npetersen2/OpenThermo/firmware/openThermo/Core/Src/drv_tmp117.c

#include "drv_tmp117.h"
#include "drv_i2c.h"
#include "drv_tmp117_registers.h"
#include <stdbool.h>

static uint8_t _deviceAddress;   // Address of Temperature sensor

static uint16_t readRegister(uint8_t reg);				// Reads 2 register bytes from sensor
static void writeRegister(uint8_t reg, uint16_t data);	// Wires single byte of data to the sensor

#define bitRead(value, bit) (((value) >> (bit)) & 0x01)
#define bitSet(value, bit) ((value) |= (1UL << (bit)))
#define bitClear(value, bit) ((value) &= ~(1UL << (bit)))
#define bitWrite(value, bit, bitvalue) (bitvalue ? bitSet(value, bit) : bitClear(value, bit))

void drv_tmp117_init(void)
{
	  // Check to see if sensor is alive
	  bool working = drv_tmp117_begin(0x48);
	  if (!working) {
		  while(1);
	  }
	  drv_tmp117_setConversionCycleBit(0);
	  drv_tmp117_setConversionAverageMode(2);
}


/* BEGIN
    This function checks if the TMP will ACK over I2C, and
	if the TMP will correctly self-identify with the proper
	device ID. This will set the address of the device along
	with setting the wire for the I2C Communication.
	This will return true if both checks pass.
*/
bool drv_tmp117_begin(uint8_t sensorAddress)
{
	_deviceAddress = sensorAddress; // Sets the address of the device

	uint16_t deviceID = readRegister(TMP117_DEVICE_ID); // reads registers into rawData

	//make sure the device ID reported by the TMP is correct
	//should always be 0x0117
	if (deviceID != DEVICE_ID_VALUE)
	{
		return false;
	}

	return true; //returns true if all the checks pass
}

/* GET ADDRESS
	This function returns the address of the device once
	called upon. This address can only be 0x48 (GND),
	0x49 (V+), 0x4A (SDA), and 0x4B (SCL)
*/
uint8_t drv_tmp117_getAddress(void)
{
	return _deviceAddress;
}

/* READ REGISTER
	This function reads the register bytes from the sensor when called upon.
	This reads 2 bytes of information from the 16-bit registers.
*/
static uint16_t readRegister(uint8_t reg)
{
	// Start by sending register across bus
	drv_i2c_tx(_deviceAddress<<1, &reg, 1);

	// Read two bytes
	uint8_t data[2] = {0};
	drv_i2c_rx(_deviceAddress<<1, data, 2);

	// Swap the LSB and the MSB
	int16_t ret = 0;
	ret = ((data[0] << 8) | data[1]);

	return ret;
}


/* WRITE REGISTER
    Wire data to a TMP117 register
*/
static void writeRegister(uint8_t reg, uint16_t data)
{
	uint8_t highByte = (data >> 8) & 0xFF;
	uint8_t lowByte = (data & 0xFF);

	drv_i2c_tx(_deviceAddress<<1, &reg, 1);
	drv_i2c_tx(_deviceAddress<<1, &highByte, 1); // Write MSB (D15-D8)
	drv_i2c_tx(_deviceAddress<<1, &lowByte, 1); // Write LSB (D7-D0)
}


/* READ TEMPERATURE CELSIUS
	This function reads the temperature reading from the sensor
	and returns the value in degrees celsius.
	NOTE: The data type of digitalTemp is a signed integer, meaning that the
	value of the binary number being read will be negative if the MSB is 1,
	and positive if the bit is 0.
*/
float drv_tmp117_readTempC(void)
{
	int16_t digitalTempC = readRegister(TMP117_TEMP_RESULT); // Calls to read registers to pull all the bits to store in an array

	float finalTempC = digitalTempC * TMP117_RESOLUTION; // Multiplies by the resolution for digital to final temp

	return finalTempC;
}

/* READ TEMPERATURE FAHRENHEIT
	This function calculates the fahrenheit reading from the
	celsius reading initially found.
	The device reads in celsius unless this function is called.
*/
float drv_tmp117_readTempF(void)
{
	return drv_tmp117_readTempC() * 9.0f / 5.0f + 32.0f; // Conversion from °C to °F
}

/* GET TEMPERATURE OFFSET
	This function reads the temperature offset. This reads from the register
	value 0x07 (TMP117_TEMP_OFFSET). This can be found on page 23 of the
	datasheet.
*/
float drv_tmp117_getTemperatureOffset(void)
{
	int16_t _offset = 0;
	_offset = readRegister(TMP117_TEMP_OFFSET);				// Reads from the temperature offset register
	float finalOffset = (float)_offset * TMP117_RESOLUTION; // Multiplies by the resolution for correct offset temperature
	return finalOffset;
}

/* SET TEMPERATURE OFFSET
	This function sets the offset temperature of the device. The user
	can write to this to set any desired offset within the temperature range.
	This writes to the register value 0x07 (TMP117_TEMP_OFFSET)
*/
void drv_tmp117_setTemperatureOffset(float offset)
{
	int16_t resolutionOffset = offset / TMP117_RESOLUTION; // Divides by the resolution to send the correct value to the sensor
	writeRegister(TMP117_TEMP_OFFSET, resolutionOffset);   // Writes to the offset temperature register with the new offset value
}

/* GET LOW LIMIT
	This function reads the low limit register that is set by the user.
	The values are signed integers since they can be negative.
*/
float drv_tmp117_getLowLimit(void)
{
	int16_t lowLimit = 0;
	lowLimit = readRegister(TMP117_T_LOW_LIMIT);			// Calls to read register to pull all the bits to store in a variable
	float finalLimit = (float)lowLimit * TMP117_RESOLUTION; // Multiplies by the resolution for correct offset temperature
	return finalLimit;
}

/* SET LOW LIMIT
	This function allows the user to set the low limit register to whatever
	specified value, as long as in the range for the temperature sensor. This
	function can be used as a threshold for Therm mode and or Alert mode.
	The values are signed integers since they can be negative.
*/
void drv_tmp117_setLowLimit(float lowLimit)
{
	int16_t finalLimit = lowLimit / TMP117_RESOLUTION; // Divides by the resolution to send the correct value to the sensor
	writeRegister(TMP117_T_LOW_LIMIT, finalLimit);	 // Writes to the low limit temperature register with the new limit value
}

/* GET HIGH LIMIT
	This function reads the high limit register that is set by the user.
	The values are signed integers since they can be negative.
*/
float drv_tmp117_getHighLimit(void)
{
	int16_t highLimit = 0;
	highLimit = readRegister(TMP117_T_HIGH_LIMIT);			 // Calls to read registers to pull all the bits to store in an array
	float finalLimit = (float)highLimit * TMP117_RESOLUTION; // Multiplies by the resolution for correct offset temperature
	return finalLimit;
}

/* SET HIGH LIMIT
	This function allows the user to set the high limit register to whatever
	specified value, as long as in the range for the temperature sensor. This
	function can be used as a threshold for Therm mode and or Alert mode
	The values are signed integers since they can be negative.
*/
void drv_tmp117_setHighLimit(float highLimit)
{
	int16_t finalLimit = highLimit / TMP117_RESOLUTION; // Divides by the resolution to send the correct value to the sensor
	writeRegister(TMP117_T_HIGH_LIMIT, finalLimit);		// Writes to the high limit temperature register with the new limit value
}

/*GET CONFIGURATION REGISTER
	This function reads configuration register. Use this function if you need to read
	certain flags before they are cleared. This can be found on page 25 of the
	datasheet.
*/
uint16_t drv_tmp117_getConfigurationRegister(void)
{
	uint16_t configReg = 0;
	configReg = readRegister(TMP117_CONFIGURATION);

	return configReg;
}

/*GET HIGH AND LOW ALERT
	This function reads configuration register and saves the high and low alert flags.
	Use this function if you need to read the alert flags before they are cleared.
	This can be found on page 25 of the datasheet.
*/
uint8_t drv_tmp117_getHighLowAlert(void)
{
	uint16_t configReg = 0;
	configReg = readRegister(TMP117_CONFIGURATION); //Grab what is in the configuration register

	uint8_t highlowAlert = 0; //temporary variable to hold high and low alert flags
	//Get high alert flag from 15th bit of the configuration register,
	//    then write bit to highlowAlert's 2nd position from the right
	bitWrite(highlowAlert, 1, bitRead(configReg, 15));

	//Get high alert flag from 14th bit of the configuration register,
	//    then write bit to highlowAlert's 1st position from the right
	bitWrite(highlowAlert, 0, bitRead(configReg, 14));

	return highlowAlert; //return high and low alert flags
}

/*GET HIGH ALERT
	This function reads the 15th bit of the configuration register to
	tell if the conversion result is higher than the high limit. This
	is set as a High Alert flag. This can be found on page 25 of the
	datasheet.
*/
bool drv_tmp117_getHighAlert(void)
{
	uint16_t configReg = 0;
	configReg = readRegister(TMP117_CONFIGURATION); //Grab what is in the configuration register

	uint8_t highAlert = bitRead(configReg, 15); // Fills with the 15th bit of the configuration register

	if (highAlert == 1)
	{
		return true;
	}
	else
	{
		return false;
	}
}

/*GET LOW ALERT
	This function reads the 14th bit of the configuration register to
	tell if the conversion result is lower than the low limit. This
	is set as a Low Alert flag. This can be found on page 25 of the
	datasheet.
*/
bool drv_tmp117_getLowAlert(void)
{
	uint16_t configReg = 0;
	configReg = readRegister(TMP117_CONFIGURATION); //Grab what is in the configuration register

	uint8_t lowAlert = bitRead(configReg, 14); // Fills with the 14th bit of the configuration register

	if (lowAlert == 1)
	{
		return true;
	}
	else
	{
		return false;
	}
}

/*SET ALERT FUNCTION MODE
	This function sets the alert function mode to either "alert" or
	"therm" mode. This can be found on page 25 of the datasheet.
*/
void drv_tmp117_setAlertFunctionMode(uint8_t setAlertMode)
{
	uint16_t AlertFunctionMode = 0;
	AlertFunctionMode = readRegister(TMP117_CONFIGURATION); // Fills mode to be the config register

	if (setAlertMode == 1) // 1: Therm mode
	{
		bitWrite(AlertFunctionMode, 4, 1); //set register bit to be 1
		writeRegister(TMP117_CONFIGURATION, AlertFunctionMode);
	}
	else // 0: alert mode
	{
		bitClear(AlertFunctionMode, 4); //set register bit to be 0
		writeRegister(TMP117_CONFIGURATION, AlertFunctionMode);
	}
}

/*GET ALERT FUNCTION MODE
	This function gets the alert function mode to either "alert" or
	"therm" mode. This can be found on page 25 of the datasheet.
*/
uint8_t drv_tmp117_getAlertFunctionMode(void)
{
	uint16_t configReg = 0;
	configReg = readRegister(TMP117_CONFIGURATION); // Fill configReg with the configuration register

	uint8_t currentAlertMode = bitRead(configReg, 4); //Get the value from the Therm/alert mode ("T/nA") select field

	if (currentAlertMode == 1) //if "therm" mode
	{
		return 1;
	}
	else //if "alert" mode
	{
		return 0;
	}
}

/* SOFTWARE RESET
	This function performs a software reset, loading all the default
	values into the configuration register. A table of the configuration
	register can be found on page 25 of the datasheet.
*/
void drv_tmp117_softReset(void)
{
	uint16_t reset = 0;
	reset = readRegister(TMP117_CONFIGURATION); // Fills mode to be the configuration register
	bitWrite(reset, 1, 1);
	writeRegister(TMP117_CONFIGURATION, reset);
}

/* SET CONTINUOUS CONVERSION MODE
	This function sets the conversion mode of the sensor to be
	continuous. This can be found in the datasheet on Page 25 Table 6.
	The TMP117 defaults to Continuous Conversion Mode on reset.
*/
void drv_tmp117_setContinuousConversionMode(void)
{
	uint16_t mode = 0;
	mode = readRegister(TMP117_CONFIGURATION); // Fills mode to be the configuration register

	bitClear(mode, 10); // Clears bit 10
	bitClear(mode, 11); // Clears bit 11
	writeRegister(TMP117_CONFIGURATION, mode);
}

/* SET SHUTDOWN MODE
	This function sets the conversion mode of the sensor to be
	in shutdown mode. This can be found in the datasheet on Page
	25 Table 6. The TMP117 defaults to Continuous Conversion Mode
	on reset.
*/
void drv_tmp117_setShutdownMode(void)
{
	uint16_t mode = 0;
	mode = readRegister(TMP117_CONFIGURATION); // Fills mode to be the configuration register

	bitClear(mode, 11);	// Clears bit 11
	bitWrite(mode, 10, 1); // Sets bit 10 to 1
	writeRegister(TMP117_CONFIGURATION, mode);
}

/* SET ONE SHOT MODE
	This function sets the conversion mode of the sensor to be
	in one shot mode. This can be found in the datasheet on Page
	25 Table 6. The TMP117 defaults to Continuous Conversion Mode
	on reset.
*/
void drv_tmp117_setOneShotMode(void)
{
	uint16_t mode = 0;
	mode = readRegister(TMP117_CONFIGURATION); // Fills mode to be the configuration register

	bitWrite(mode, 10, 1); // Sets bit 10 to 1
	bitWrite(mode, 11, 1); // Sets bit 11 to 1
	writeRegister(TMP117_CONFIGURATION, mode);
}

/* GET CONVERSION MODE
	This function reads the mode for the conversions, then
	prints it to the Serial Monitor in the Arduino IDE.
	This can be found in the datasheet on Page 25 Table 6.
	This function can return Continuous Conversion Mode (1),
	Shutdown Mode (2), and One-Shot Mode (3). This should never
	return 4 (the other continuous conversion) since there is
	no function for writing to the value.
*/
uint8_t drv_tmp117_getConversionMode(void)
{
	uint16_t configReg = 0;
	configReg = readRegister(TMP117_CONFIGURATION); // Fill configReg with the configuration register

	uint8_t currentMode1 = bitRead(configReg, 11); // Left most conversion bit
	uint8_t currentMode2 = bitRead(configReg, 10); // Right most conversion bit

	if ((currentMode1 == 0) && (currentMode2 == 0)) // 0b00, Continuous Conversion Mode
	{
		return 1; // Actually 0, but return 1 for the example sketch
	}
	else if ((currentMode1 == 1) && (currentMode2 == 0)) // 0b10, should not be set this
	{
		return 4; // This value should never be returned
	}
	else if ((currentMode1 == 0) && (currentMode2 == 1)) // 0b01, Shutdown Mode
	{
		return 2; // Actually 0b01, but return 2 for the example sketch
	}
	else if ((currentMode1 == 1) && (currentMode2 == 1)) // 0b11, One-Shot Mode
	{
		return 3;
	}
	else
	{
		return 1; //Default
	}
}

/*SET CONVERSION AVERAGE MODE
	This function sets the conversion averaging mode of the device
	when in Continuous Conversion Mode. This can be found on page
	25 of the TMP117 datasheet.
 */
void drv_tmp117_setConversionAverageMode(uint8_t convMode)
{
	uint16_t mode = 0;
	mode = readRegister(TMP117_CONFIGURATION); // Fills to be the config register

	if (convMode == 0) // No Averaging, 0b00
	{
		bitClear(mode, 5); // Clears bit 5
		bitClear(mode, 6); // Clears bit 6
		writeRegister(TMP117_CONFIGURATION, mode);
	}
	else if (convMode == 1) // 8 Averaged Conversions, 0b01
	{
		bitClear(mode, 6);	// Clears bit 6
		bitWrite(mode, 5, 1); // Sets bit 5 to be 1
		writeRegister(TMP117_CONFIGURATION, mode);
	}
	else if (convMode == 2) // 32 Averaged Conversions, 0b10
	{
		bitWrite(mode, 6, 1); // Sets bit 6 to be 1
		bitClear(mode, 5);	// Clears bit 5
		writeRegister(TMP117_CONFIGURATION, mode);
	}
	else if (convMode == 3) // 64 Averaged Conversions, 0b11
	{
		bitWrite(mode, 6, 1); // Sets bit 6 to be 1
		bitWrite(mode, 5, 1); // Sets bit 5 to be 1
		writeRegister(TMP117_CONFIGURATION, mode);
	}
}

/*GET CONVERSION AVERAGE MODE
	This function reads for the averaging mode of the conversions,
	then prints it to the Serial Monitor in the Arduino IDE.
	This can be found in the datasheet on Page 25 Table 6.
 */
uint8_t drv_tmp117_getConversionAverageMode(void)
{
	uint16_t configReg = 0;
	configReg = readRegister(TMP117_CONFIGURATION); // Fills configReg with config register values

	uint8_t currentMode6 = bitRead(configReg, 6); // Left most averaging bit
	uint8_t currentMode5 = bitRead(configReg, 5); // Right most averaging bit

	if ((currentMode6 == 0) && (currentMode5 == 0)) // 0b00, no averaging
	{
		return 0b00;
	}
	else if ((currentMode6 == 0) && (currentMode5 == 1)) // 0b01, 8 averaged conversions
	{
		return 0b01;
	}
	else if ((currentMode6 == 1) && (currentMode5 == 0)) // 0b10, 32 averaged conversions
	{
		return 0b10;
	}
	else if ((currentMode6 == 1) && (currentMode5 == 1)) // 0b11, 64 averaged conversions
	{
		return 0b11;
	}
	else
	{
		return 0b00; //No averaging
	}
}

/* SET CONVERSION CYCLE BIT
	This function sets the conversion cycle time bit in
	Continuous Conversion mode. The times for the conversions
	can be found below or in the datasheet on Page 25 Table
	6 or on Page 27 Table 7. The user puts in 0-7 and it will
	return the cycle time accoring to the values in the chart.
 	  Conversion Cycle Time in CC Mode (found on the datasheet page 26 table 6)
               AVG       0       1       2       3
       CONV  averaging  (0)     (8)     (32)   (64)
         0             15.5ms  125ms   500ms    1s
         1             125ms   125ms   500ms    1s
         2             250ms   250ms   500ms    1s
         3             500ms   500ms   500ms    1s
         4             1s      1s      1s       1s
         5             4s      4s      4s       4s
         6             8s      8s      8s       8s
         7             16s     16s     16s      16s
 */
void drv_tmp117_setConversionCycleBit(uint8_t convTime)
{
	uint16_t mode = 0;
	mode = readRegister(TMP117_CONFIGURATION); // Fills in time to be the config register

	if (convTime == 0) // 0b000
	{
		bitClear(mode, 9); // Clears bit 9
		bitClear(mode, 8); // Clears bit 8
		bitClear(mode, 7); // Clears bit 7
		writeRegister(TMP117_CONFIGURATION, mode);
	}
	else if (convTime == 1) // 0b001
	{
		bitClear(mode, 9);	// Clears bit 9
		bitClear(mode, 8);	// Clears bit 8
		bitWrite(mode, 7, 1); // Sets bit 7 to be 1
		writeRegister(TMP117_CONFIGURATION, mode);
	}
	else if (convTime == 2) // 0b010
	{
		bitClear(mode, 9);	// Clears bit 9
		bitWrite(mode, 8, 1); // Sets bit 8 to be 1
		bitClear(mode, 7);	// Clears bit 7
		writeRegister(TMP117_CONFIGURATION, mode);
	}
	else if (convTime == 3) // 0b011
	{
		bitClear(mode, 9);	// Clears bit 9
		bitWrite(mode, 8, 1); // Sets bit 8 to be 1
		bitWrite(mode, 7, 1); // Sets bit 7 to be 1
		writeRegister(TMP117_CONFIGURATION, mode);
	}
	else if (convTime == 4) // 0b100
	{
		bitWrite(mode, 9, 1); // Sets bit 9 to be 1
		bitClear(mode, 8);	// Clears bit 8
		bitClear(mode, 7);	// Clears bit 7
		writeRegister(TMP117_CONFIGURATION, mode);
	}
	else if (convTime == 5) // 0b101
	{
		bitWrite(mode, 9, 1); // Sets bit 9 to be 1
		bitClear(mode, 8);	// Clears bit 8
		bitWrite(mode, 7, 1); // Sets bit 7 to be 1
		writeRegister(TMP117_CONFIGURATION, mode);
	}
	else if (convTime == 6) // 0b110
	{
		bitWrite(mode, 9, 1); // Sets bit 9 to be 1
		bitWrite(mode, 8, 1); // Sets bit 8 to be 1
		bitClear(mode, 7);	// Clears bit 7
		writeRegister(TMP117_CONFIGURATION, mode);
	}
	else if (convTime == 7) // 0b111
	{
		bitWrite(mode, 9, 1); // Sets bit 9 to be 1
		bitWrite(mode, 8, 1); // Sets bit 8 to be 1
		bitWrite(mode, 7, 1); // Sets bit 7 to be 1
		writeRegister(TMP117_CONFIGURATION, mode);
	}
}

/* GET CONVERSION CYCLE BIT
	This function returns the Conversion Cycle Bit value that the
	device is currently in at the time. This bit can help determine
	the conversion cycle time that the device is in while being in
	continuous conversion mode.
 	  Conversion Cycle Time in CC Mode (found on the datasheet page 26 table 6)
               AVG       0       1       2       3
       CONV  averaging  (0)     (8)     (32)   (64)
         0             15.5ms  125ms   500ms    1s
         1             125ms   125ms   500ms    1s
         2             250ms   250ms   500ms    1s
         3             500ms   500ms   500ms    1s
         4             1s      1s      1s       1s
         5             4s      4s      4s       4s
         6             8s      8s      8s       8s
         7             16s     16s     16s      16s
*/
uint8_t drv_tmp117_getConversionCycleBit(void)
{
	uint16_t configReg = 0;
	configReg = readRegister(TMP117_CONFIGURATION); // Fills configReg with config register values

	uint8_t currentTime9 = bitRead(configReg, 9); // Left most bit (9)
	uint8_t currentTime8 = bitRead(configReg, 8); // Middle bit (8)
	uint8_t currentTime7 = bitRead(configReg, 7); // Right most bit (7)

	if ((currentTime9 == 0) && (currentTime8 == 0) && (currentTime7 == 0)) // 0b000
	{
		return 0b000;
	}
	else if ((currentTime9 == 0) && (currentTime8 == 0) && (currentTime7 == 1)) // 0b001
	{
		return 0b001;
	}
	else if ((currentTime9 == 0) && (currentTime8 == 1) && (currentTime7 == 0)) // 0b010
	{
		return 0b010;
	}
	else if ((currentTime9 == 0) && (currentTime8 == 1) && (currentTime7 == 1)) // 0b011
	{
		return 0b011;
	}
	else if ((currentTime9 == 1) && (currentTime8 == 0) && (currentTime7 == 0)) // 0b100
	{
		return 0b100;
	}
	else if ((currentTime9 == 1) && (currentTime8 == 0) && (currentTime7 == 1)) // 0b101
	{
		return 0b101;
	}
	else if ((currentTime9 == 1) && (currentTime8 == 1) && (currentTime7 == 0)) // 0b110
	{
		return 0b110;
	}
	else if ((currentTime9 == 1) && (currentTime8 == 1) && (currentTime7 == 1)) // 0b111
	{
		return 0b111;
	}
	else
	{
		return 0b000; //Default
	}
}

/* DATA READY
	This function checks to see if there is data ready to be sent
	from the TMP117. This can be found in Page 25 Table 6 of the
	data sheet.
*/
bool drv_tmp117_dataReady(void)
{
	uint16_t response = readRegister(TMP117_CONFIGURATION);

	// If statement to see if the 13th bit of the register is 1 or not
	if (response & 1 << 13)
	{
		return true;
	}
	else
	{
		return false;
	}
}
