npetersen2/OpenThermo/firmware/openThermo/Core/Src/drv_adc.c

#include "drv_adc.h"
#include "platform.h"
#include "defines.h"
#include <stdint.h>

static ADC_HandleTypeDef hadc1;

static void MX_ADC1_Init(void);

void drv_adc_init(void)
{
	MX_ADC1_Init();
}

uint32_t drv_adc_sample(void)
{
	HAL_ADC_Start(&hadc1);
	HAL_ADC_PollForConversion(&hadc1, 1000);
	return HAL_ADC_GetValue(&hadc1);
}


/**
  * @brief ADC1 Initialization Function
  * @param None
  * @retval None
  */
static void MX_ADC1_Init(void)
{

  ADC_ChannelConfTypeDef sConfig = {0};

  // Configure the global features of the ADC (Clock, Resolution, Data Alignment and number of conversion)
  hadc1.Instance = ADC1;
  hadc1.Init.ClockPrescaler = ADC_CLOCK_SYNC_PCLK_DIV2;
  hadc1.Init.Resolution = ADC_RESOLUTION_12B;
  hadc1.Init.DataAlign = ADC_DATAALIGN_RIGHT;
  hadc1.Init.ScanConvMode = ADC_SCAN_DISABLE;
  hadc1.Init.EOCSelection = ADC_EOC_SINGLE_CONV;
  hadc1.Init.LowPowerAutoWait = DISABLE;
  hadc1.Init.LowPowerAutoPowerOff = DISABLE;
  hadc1.Init.ContinuousConvMode = DISABLE;
  hadc1.Init.NbrOfConversion = 1;
  hadc1.Init.DiscontinuousConvMode = DISABLE;
  hadc1.Init.ExternalTrigConv = ADC_SOFTWARE_START;
  hadc1.Init.ExternalTrigConvEdge = ADC_EXTERNALTRIGCONVEDGE_NONE;
  hadc1.Init.DMAContinuousRequests = DISABLE;
  hadc1.Init.Overrun = ADC_OVR_DATA_PRESERVED;
  hadc1.Init.SamplingTimeCommon1 = ADC_SAMPLETIME_3CYCLES_5;
  hadc1.Init.SamplingTimeCommon2 = ADC_SAMPLETIME_3CYCLES_5;
  hadc1.Init.OversamplingMode = DISABLE;
  hadc1.Init.TriggerFrequencyMode = ADC_TRIGGER_FREQ_HIGH;

  if (HAL_ADC_Init(&hadc1) != HAL_OK) {
	  PANIC;
  }

  // Configure Regular Channel
  sConfig.Channel = ADC_CHANNEL_1;
  sConfig.Rank = ADC_REGULAR_RANK_1;
  sConfig.SamplingTime = ADC_SAMPLINGTIME_COMMON_1;
  if (HAL_ADC_ConfigChannel(&hadc1, &sConfig) != HAL_OK) {
	  PANIC;
  }
}
